TeamScheire/schermtijd/doosontwerp/lasercut/3mm-plexi/lade/valse-bodem.dxf

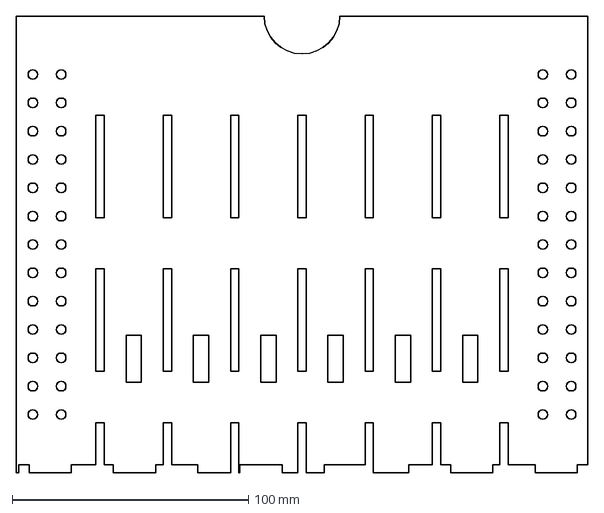
[picture p27: CAD file, 2019-09-13]
doosontwerp/lasercut/3mm-plexi/lade/valse-bodem.dxf
242.0 x 193.5 mm
