TeamScheire/schermtijd/doosontwerp/lasercut/3mm/export-valse-achterkant.dxf

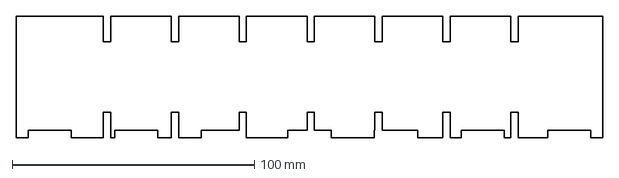
[picture p29: CAD file, 2019-09-05]
doosontwerp/lasercut/3mm/export-valse-achterkant.dxf
242.0 x 50.0 mm
