TeamScheire/schermtijd/doosontwerp/lasercut/4mm/export-tussenschot-voorkant.dxf

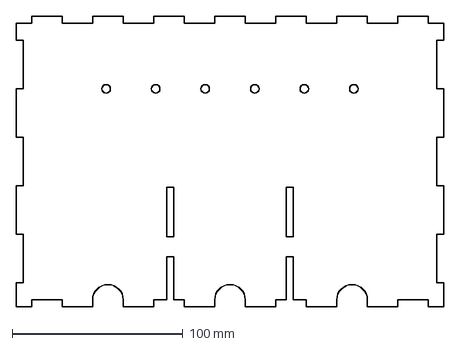
[picture p30: CAD file, 2019-08-23]
doosontwerp/lasercut/4mm/export-tussenschot-voorkant.dxf
250.0 x 170.0 mm
