TeamScheire/schermtijd/doosontwerp/lasercut/6mm/export-bodem.dxf

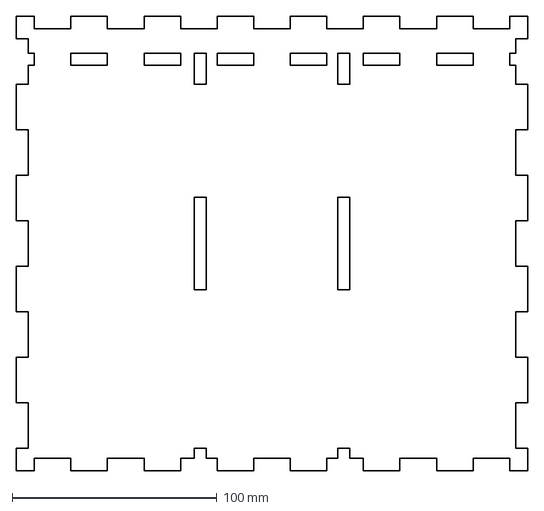
[picture p31: CAD file, 2019-08-23]
doosontwerp/lasercut/6mm/export-bodem.dxf
250.0 x 222.0 mm
