TeamScheire/schermtijd/doosontwerp/3D-print/gsmslot-verkleiner-3mm.stl

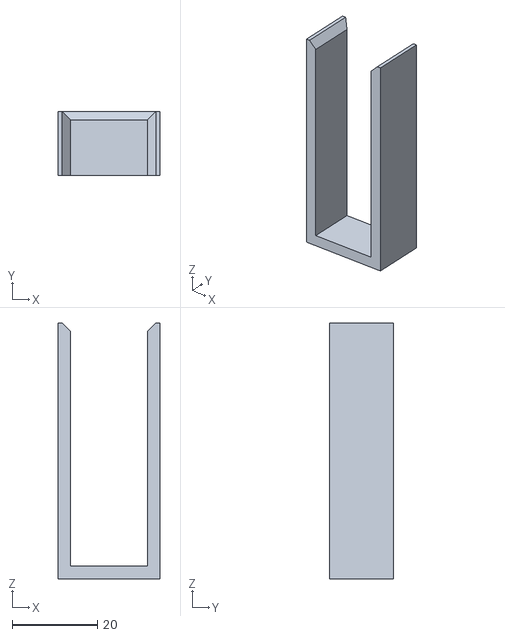
[picture p32: CAD file, 2019-08-25]
doosontwerp/3D-print/gsmslot-verkleiner-3mm.stl
24.0 x 15.0 x 60.0
