TeamScheire/schermtijd/doosontwerp/lasercut/3mm-plexi/links.dxf

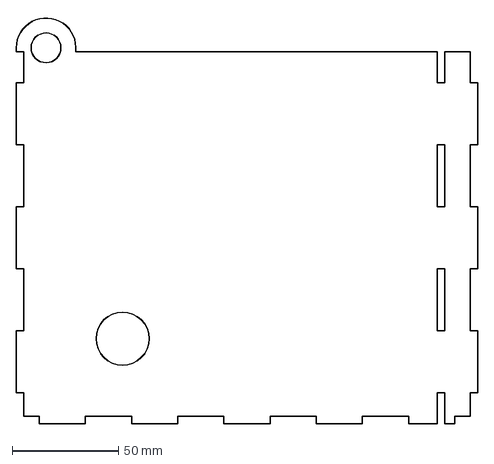
[picture p33: CAD file, 2019-09-13]
doosontwerp/lasercut/3mm-plexi/links.dxf
217.0 x 191.6 mm
