TeamScheire/schermtijd/doosontwerp/lasercut/3mm/export-voorkant.dxf

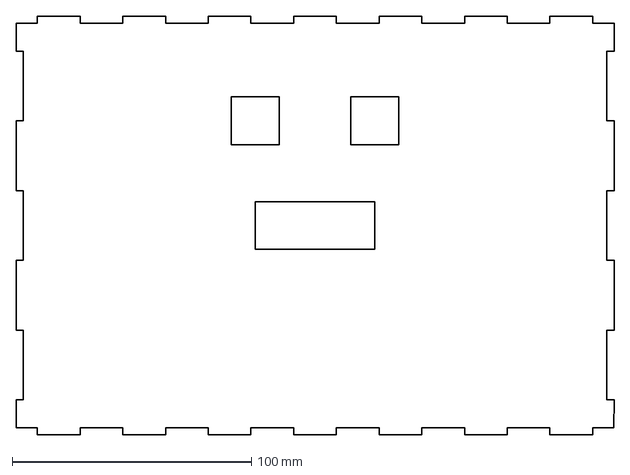
[picture p34: CAD file, 2019-09-05]
doosontwerp/lasercut/3mm/export-voorkant.dxf
250.0 x 175.0 mm
