TeamScheire/schermtijd/doosontwerp/lasercut/4mm/export-tussenschot-bovenkant.dxf

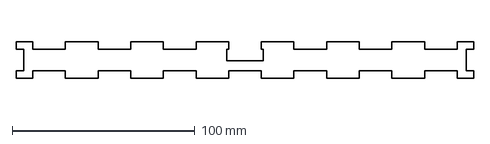
[picture p35: CAD file, 2019-08-23]
doosontwerp/lasercut/4mm/export-tussenschot-bovenkant.dxf
250.0 x 20.0 mm
