TeamScheire/schermtijd/doosontwerp/lasercut/6mm/export-gsm-schot.dxf

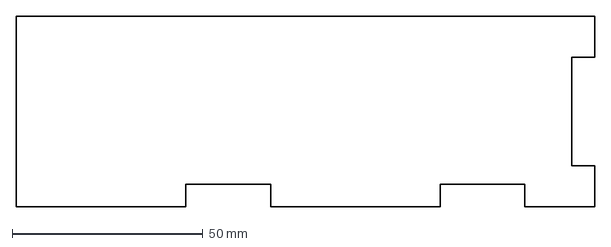
[picture p36: CAD file, 2019-08-23]
doosontwerp/lasercut/6mm/export-gsm-schot.dxf
151.5 x 50.0 mm
