TeamScheire/schermtijd/doosontwerp/3D-print/gsmslot-verkleiner-2mm.stl

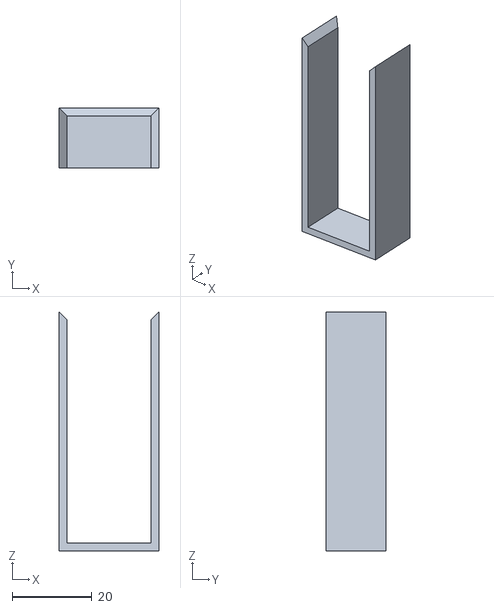
[picture p37: CAD file, 2019-08-22]
doosontwerp/3D-print/gsmslot-verkleiner-2mm.stl
25.0 x 15.0 x 60.0
