TeamScheire/schermtijd/doosontwerp/lasercut/3mm-plexi/tussenschot-voorkant.dxf

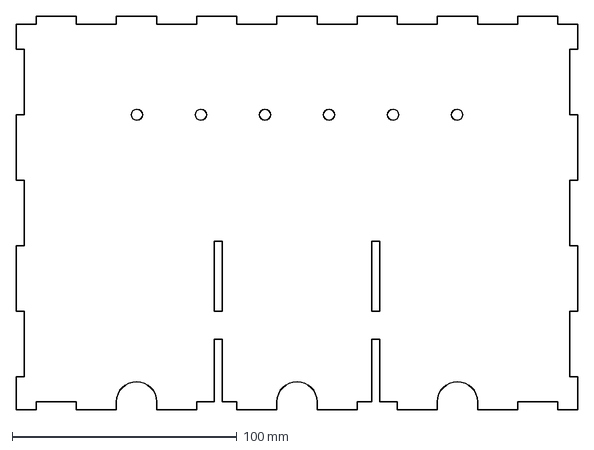
[picture p38: CAD file, 2019-09-13]
doosontwerp/lasercut/3mm-plexi/tussenschot-voorkant.dxf
250.0 x 175.0 mm
