TeamScheire/schermtijd/doosontwerp/lasercut/3mm/export-valse-bodem.dxf

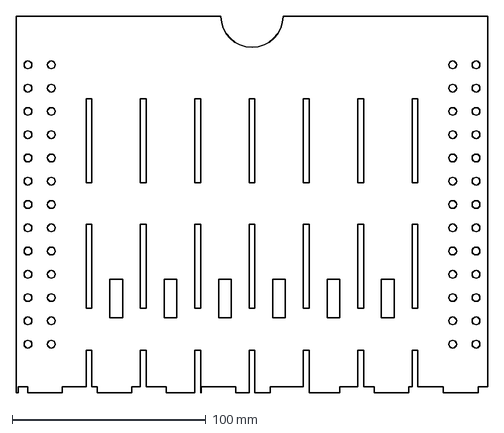
[picture p39: CAD file, 2019-09-05]
doosontwerp/lasercut/3mm/export-valse-bodem.dxf
243.0 x 194.0 mm
