TeamScheire/schermtijd/doosontwerp/lasercut/4mm/export-rechts.dxf

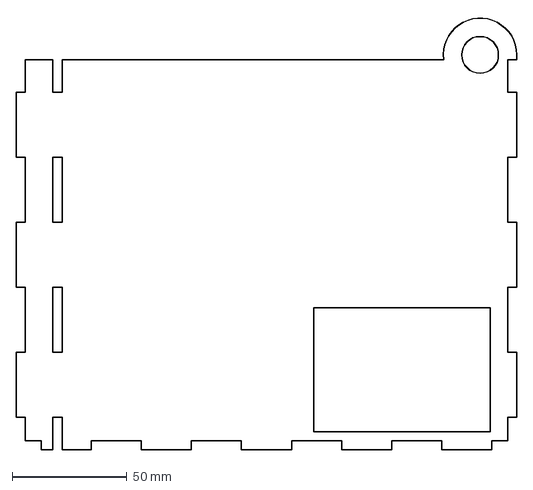
[picture p40: CAD file, 2019-08-23]
doosontwerp/lasercut/4mm/export-rechts.dxf
218.0 x 188.9 mm
