TeamScheire/schermtijd/doosontwerp/lasercut/6mm/export-valse-bodem.dxf

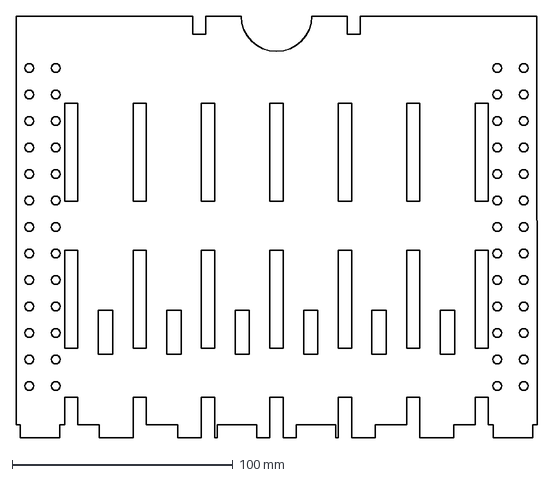
[picture p41: CAD file, 2019-08-23]
doosontwerp/lasercut/6mm/export-valse-bodem.dxf
236.0 x 191.0 mm
