TeamScheire/schermtijd/doosontwerp/3D-print/microswitch-houder.stl

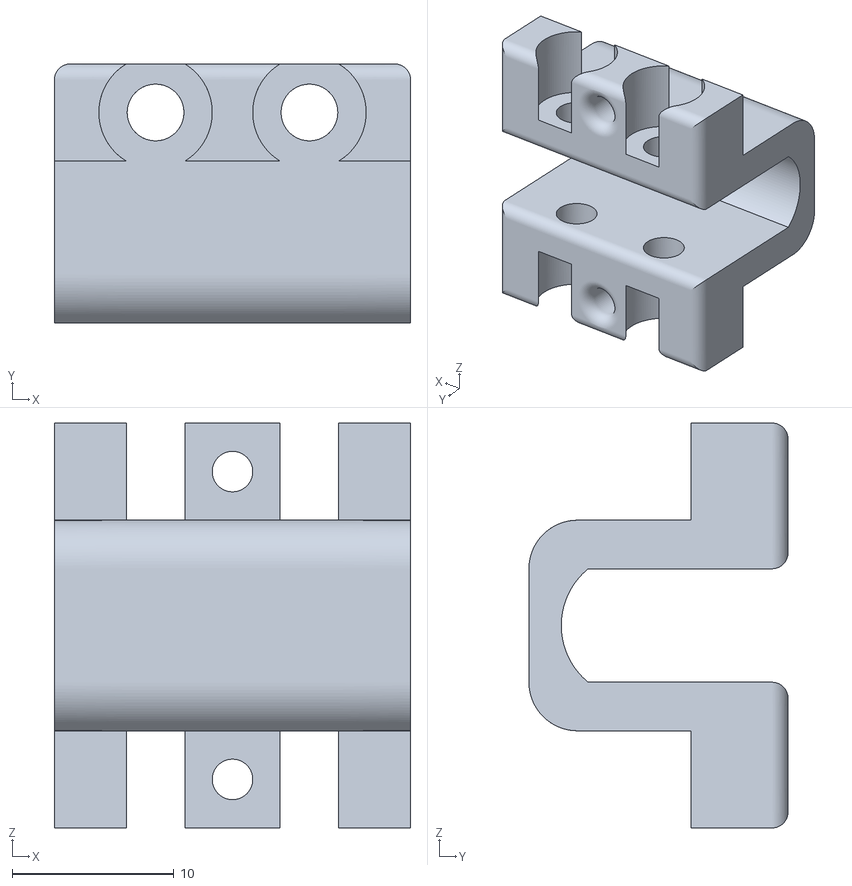
[picture p42: CAD file, 2019-08-22]
doosontwerp/3D-print/microswitch-houder.stl
22.0 x 16.0 x 25.0
