TeamScheire/schermtijd/doosontwerp/lasercut/3mm-plexi/rechts.dxf

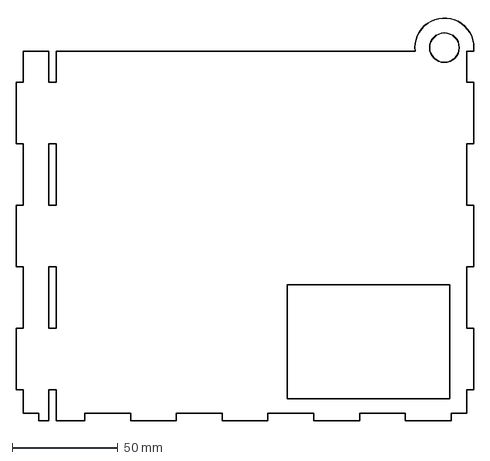
[picture p43: CAD file, 2019-09-13]
doosontwerp/lasercut/3mm-plexi/rechts.dxf
217.0 x 191.6 mm
