TeamScheire/schermtijd/doosontwerp/lasercut/3mm/export-gsm-schot.dxf

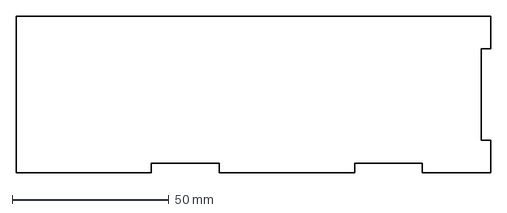
[picture p44: CAD file, 2019-09-05]
doosontwerp/lasercut/3mm/export-gsm-schot.dxf
151.5 x 50.0 mm
