TeamScheire/schermtijd/doosontwerp/lasercut/4mm/export-bodem.dxf

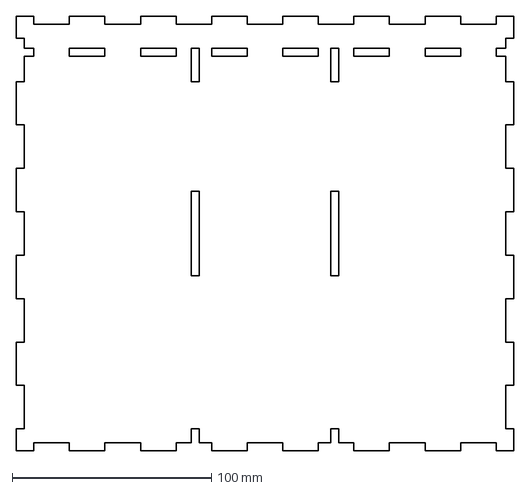
[picture p45: CAD file, 2019-08-23]
doosontwerp/lasercut/4mm/export-bodem.dxf
250.0 x 218.0 mm
