TeamScheire/schermtijd/doosontwerp/lasercut/6mm/export-top.dxf

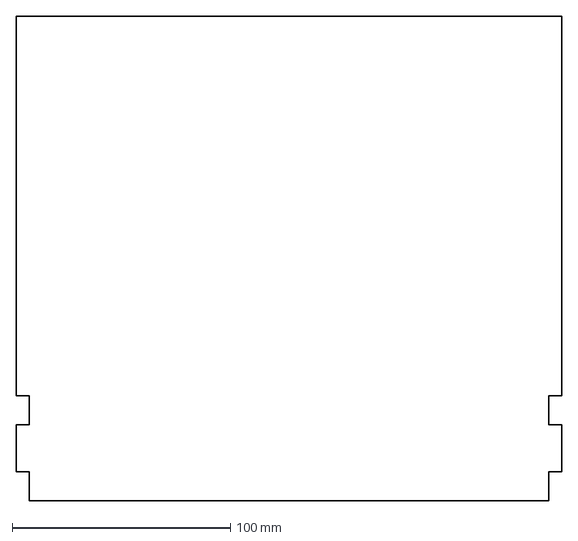
[picture p46: CAD file, 2019-08-23]
doosontwerp/lasercut/6mm/export-top.dxf
250.0 x 222.0 mm
