TeamScheire/schermtijd/doosontwerp/lasercut/3mm-plexi/achterkant.dxf

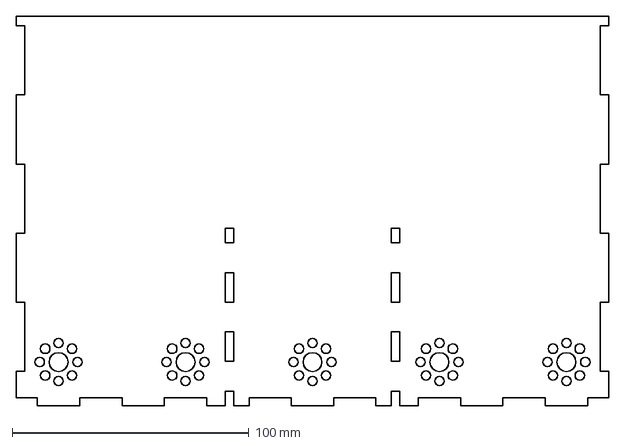
[picture p47: CAD file, 2019-09-13]
doosontwerp/lasercut/3mm-plexi/achterkant.dxf
250.0 x 164.5 mm
