TeamScheire/schermtijd/doosontwerp/lasercut/3mm/export-links.dxf

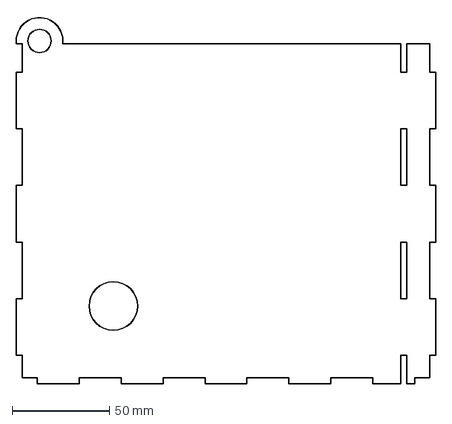
[picture p48: CAD file, 2019-09-05]
doosontwerp/lasercut/3mm/export-links.dxf
216.0 x 189.2 mm
