TeamScheire/schermtijd/doosontwerp/lasercut/4mm/export-valse-achterkant.dxf

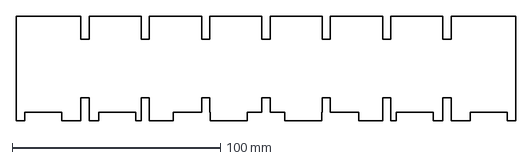
[picture p49: CAD file, 2019-08-23]
doosontwerp/lasercut/4mm/export-valse-achterkant.dxf
240.0 x 50.0 mm
