TeamScheire/schermtijd/doosontwerp/lasercut/6mm/export-voorkant.dxf

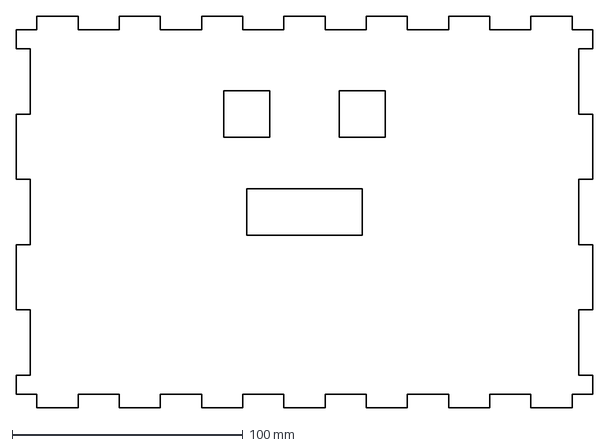
[picture p50: CAD file, 2019-08-23]
doosontwerp/lasercut/6mm/export-voorkant.dxf
250.0 x 170.0 mm
