TeamScheire/schermtijd/doosontwerp/lasercut/3mm-plexi/bodem.dxf

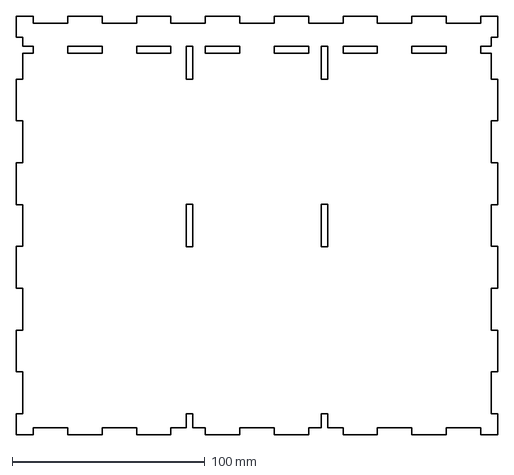
[picture p51: CAD file, 2019-09-13]
doosontwerp/lasercut/3mm-plexi/bodem.dxf
250.0 x 217.0 mm
