TeamScheire/schermtijd/doosontwerp/lasercut/3mm/export-achterkant.dxf

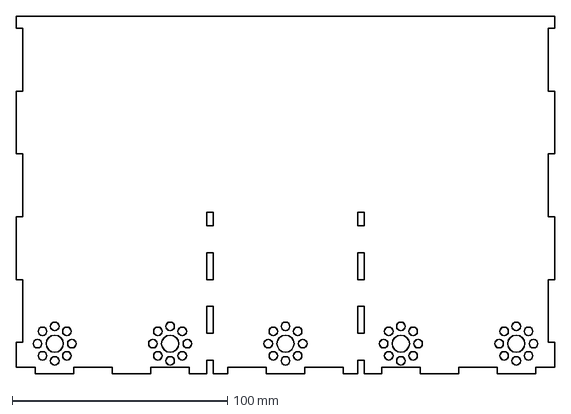
[picture p52: CAD file, 2019-09-05]
doosontwerp/lasercut/3mm/export-achterkant.dxf
250.0 x 166.0 mm
