TeamScheire/schermtijd/doosontwerp/lasercut/4mm/export-links.dxf

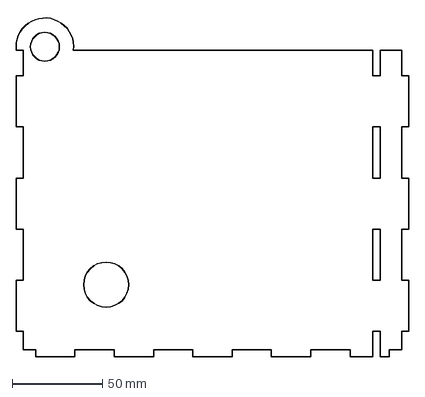
[picture p53: CAD file, 2019-08-23]
doosontwerp/lasercut/4mm/export-links.dxf
218.0 x 188.9 mm
