TeamScheire/schermtijd/doosontwerp/lasercut/6mm/export-tussenschot-bovenkant.dxf

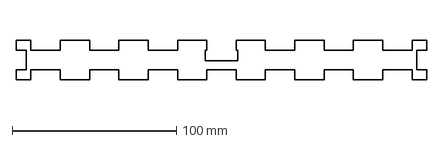
[picture p54: CAD file, 2019-08-23]
doosontwerp/lasercut/6mm/export-tussenschot-bovenkant.dxf
250.0 x 24.0 mm
