TeamScheire/schermtijd/doosontwerp/lasercut/3mm-plexi/top.dxf

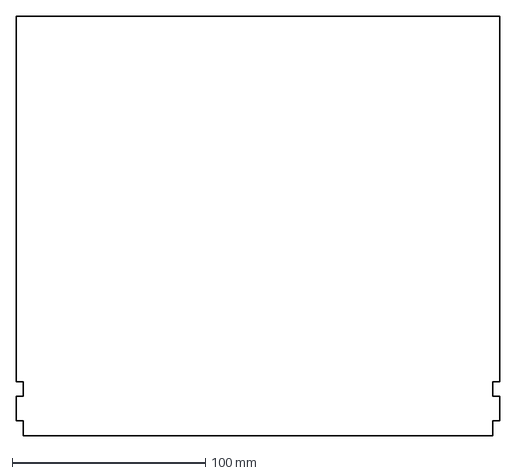
[picture p55: CAD file, 2019-09-13]
doosontwerp/lasercut/3mm-plexi/top.dxf
250.0 x 217.0 mm
