TeamScheire/schermtijd/doosontwerp/lasercut/3mm/export-tussenschot.dxf

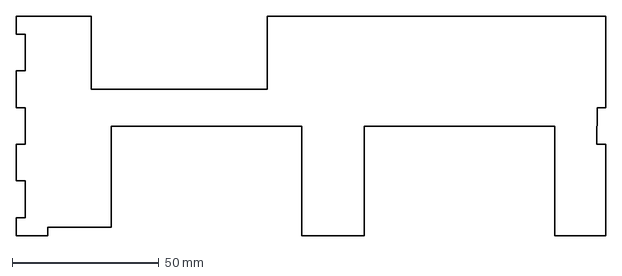
[picture p56: CAD file, 2019-09-05]
doosontwerp/lasercut/3mm/export-tussenschot.dxf
201.0 x 75.0 mm
