TeamScheire/schermtijd/doosontwerp/lasercut/4mm/export-gsm-schot.dxf

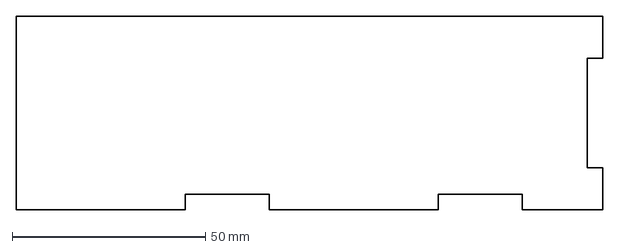
[picture p57: CAD file, 2019-08-23]
doosontwerp/lasercut/4mm/export-gsm-schot.dxf
151.5 x 50.0 mm
