TeamScheire/schermtijd/doosontwerp/lasercut/6mm/export-valse-achterkant.dxf

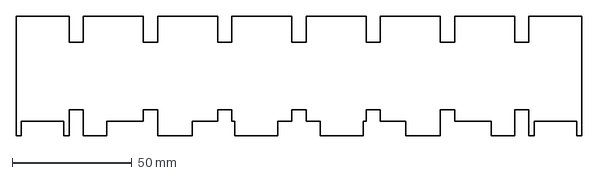
[picture p58: CAD file, 2019-08-23]
doosontwerp/lasercut/6mm/export-valse-achterkant.dxf
236.0 x 50.0 mm
