TeamScheire/schermtijd/doosontwerp/lasercut/3mm/export-bodem.dxf

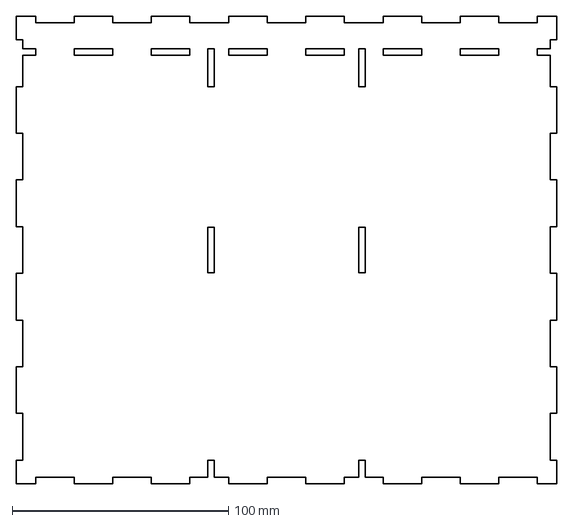
[picture p59: CAD file, 2019-08-29]
doosontwerp/lasercut/3mm/export-bodem.dxf
250.0 x 216.0 mm
