TeamScheire/schermtijd/doosontwerp/lasercut/4mm/export-top.dxf

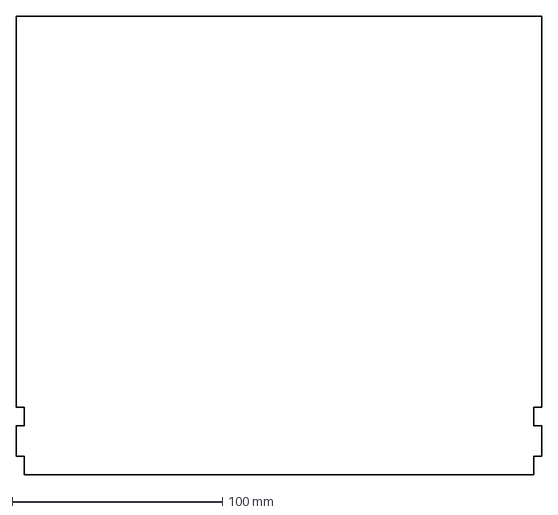
[picture p60: CAD file, 2019-08-23]
doosontwerp/lasercut/4mm/export-top.dxf
250.0 x 218.0 mm
