TeamScheire/schermtijd/doosontwerp/lasercut/6mm/export-tussenschot-voorkant.dxf

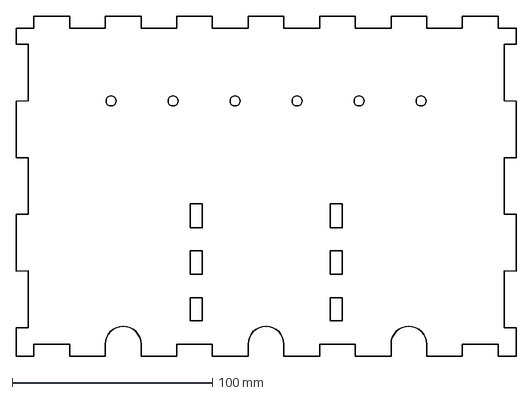
[picture p61: CAD file, 2019-08-23]
doosontwerp/lasercut/6mm/export-tussenschot-voorkant.dxf
250.0 x 170.0 mm
