TeamScheire/schermtijd/doosontwerp/lasercut/3mm/export-tussenschot-bovenkant.dxf

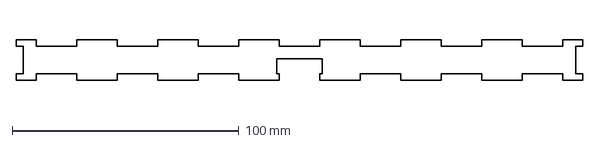
[picture p62: CAD file, 2019-08-29]
doosontwerp/lasercut/3mm/export-tussenschot-bovenkant.dxf
250.0 x 18.0 mm
