TeamScheire/schermtijd/doosontwerp/lasercut/6mm/export-rechts.dxf

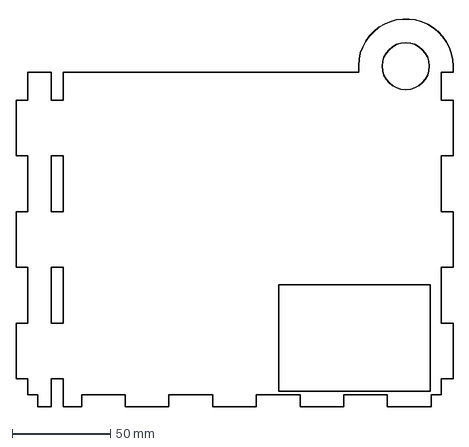
[picture p64: CAD file, 2019-08-23]
doosontwerp/lasercut/6mm/export-rechts.dxf
222.0 x 198.4 mm
