TeamScheire/schermtijd/doosontwerp/lasercut/3mm/export-top.dxf

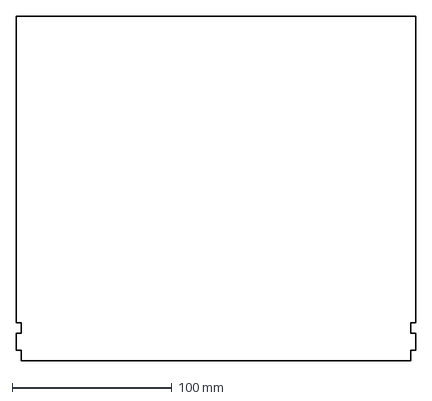
[picture p65: CAD file, 2019-08-29]
doosontwerp/lasercut/3mm/export-top.dxf
250.0 x 216.0 mm
