TeamScheire/schermtijd/doosontwerp/lasercut/4mm/export-valse-bodem.dxf

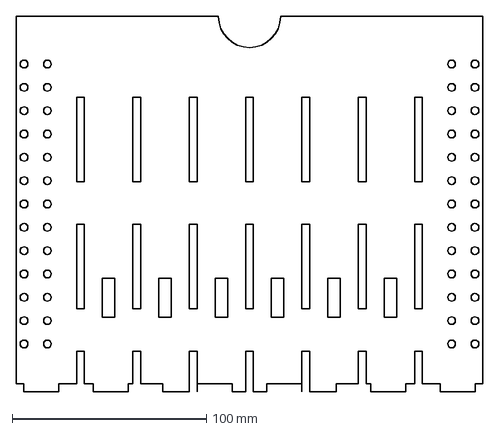
[picture p66: CAD file, 2019-08-23]
doosontwerp/lasercut/4mm/export-valse-bodem.dxf
240.0 x 193.0 mm
