TeamScheire/schermtijd/doosontwerp/lasercut/6mm/export-links.dxf

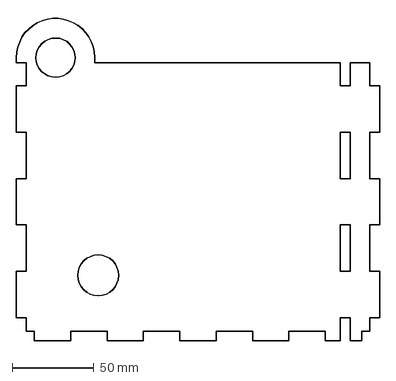
[picture p67: CAD file, 2019-08-23]
doosontwerp/lasercut/6mm/export-links.dxf
222.0 x 198.4 mm
