TeamScheire/schermtijd/doosontwerp/lasercut/3mm/export-gsm-slot.dxf

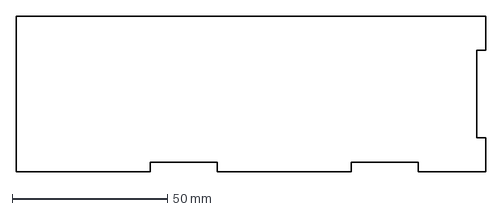
[picture p68: CAD file, 2019-08-23]
doosontwerp/lasercut/3mm/export-gsm-slot.dxf
151.5 x 50.0 mm
